joshajohnson/louise/mechanical/louise-production-dxf/5and6.dxf

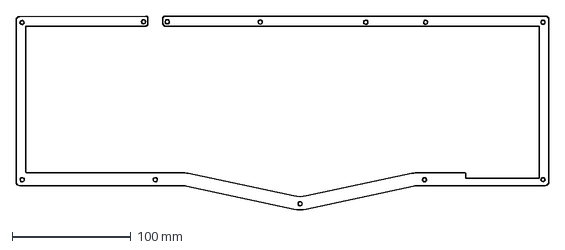
[picture p16: CAD file, 2022-07-13]
mechanical/louise-production-dxf/5and6.dxf
449.7 x 163.5 mm
