joshajohnson/louise/mechanical/louise-production-dxf/25.dxf

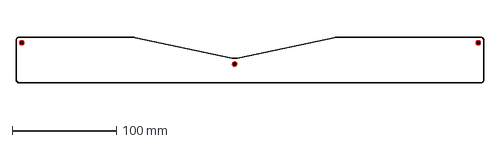
[picture p17: CAD file, 2022-07-13]
mechanical/louise-production-dxf/25.dxf
449.6 x 44.0 mm
