joshajohnson/louise/mechanical/louise-production-dxf/3-pom.dxf

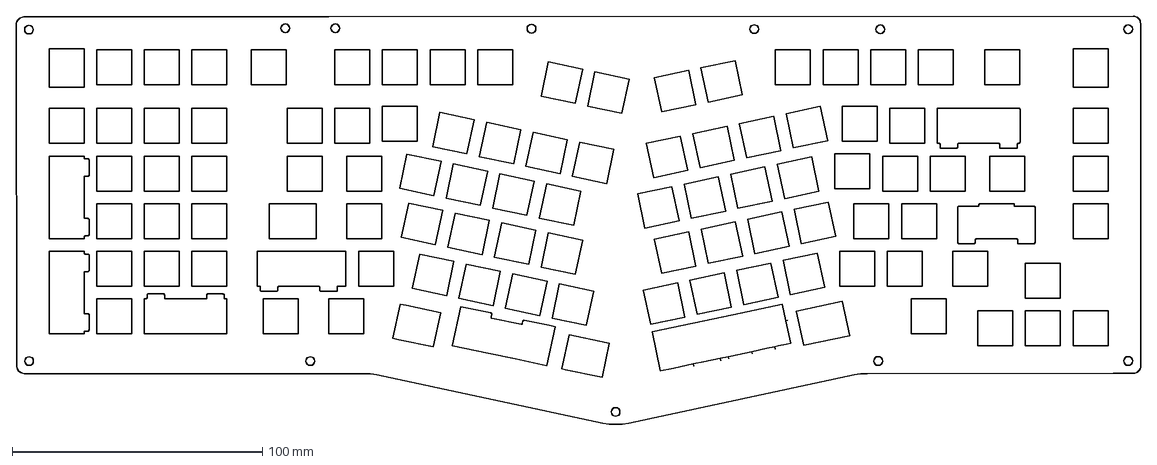
[picture p18: CAD file, 2022-07-13]
mechanical/louise-production-dxf/3-pom.dxf
449.7 x 163.5 mm
