joshajohnson/louise/mechanical/louise-production-dxf/9.dxf

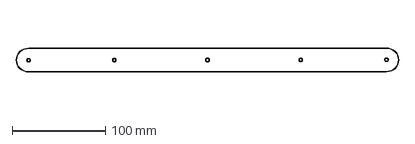
[picture p19: CAD file, 2022-07-13]
mechanical/louise-production-dxf/9.dxf
410.1 x 25.3 mm
