joshajohnson/louise/mechanical/louise-production-dxf/3-5-foam.dxf

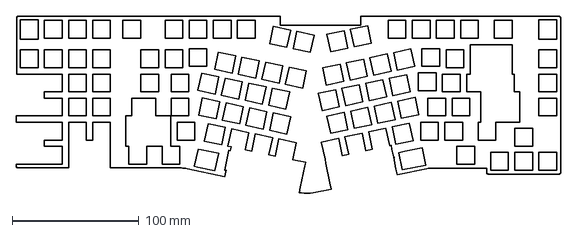
[picture p20: CAD file, 2022-07-13]
mechanical/louise-production-dxf/3-5-foam.dxf
429.7 x 140.1 mm
